skybrian/accordionsynth/sound.h

#include "midi.h"
#include <Audio.h>
#include <AudioStream.h>

namespace sound {

const float cent = 1.0005777;

#define WAVE_COUNT 2
const float detune[WAVE_COUNT] = {-cent*cent, cent*cent};

class Reed {
public:
  Reed(midi::Note n) : note(n) {
    for (int i = 0; i < WAVE_COUNT; i++) {
      waves[i].amplitude(1.0);
      waves[i].frequency(n.frequency() * detune[i]);
      env[i].attack(40);
      env[i].decay(0);
      env[i].sustain(1.0);
      env[i].release(40);
    }
    for (int i = 0; i < WAVE_COUNT; i++) {
      mixer.gain(i, 0.5/WAVE_COUNT);
    }
  }

  bool isActive() {
    return env[0].isActive();
  }

  bool isSustain() {
    return env[0].isSustain();
  }

  bool noteOn() {
    if (isActive()) {
      return false;
    }
    AudioNoInterrupts();
    for (int i = 0; i < WAVE_COUNT; i++) {
      // Start detuned saws slightly out of phase.
      // This doesn't work by default due to a bug:
      // https://github.com/PaulStoffregen/Audio/issues/312
      // I edited the code directly:
      // /Applications/Arduino.app/Contents/Java/hardware/teensy/avr/libraries/Audio/synth_waveform.h
      waves[i].begin(WAVEFORM_SAWTOOTH);
      waves[i].phase(i*20);
      env[i].noteOn();
    }
    AudioInterrupts();
    return true;
  }

  void noteOff() {
    for (int i = 0; i < WAVE_COUNT; i++) {
      env[i].noteOff();
    }
  }

  AudioStream& out() {
    return mixer; 
  }

  midi::Note note;
private:
  AudioSynthWaveform waves[WAVE_COUNT];
  AudioEffectEnvelope env[WAVE_COUNT];
  AudioMixer4 mixer;
  AudioConnection wavePatches[WAVE_COUNT] = {
    AudioConnection(waves[0], 0, env[0], 0),
    AudioConnection(waves[1], 0, env[1], 0),
  };
  AudioConnection envPatches[WAVE_COUNT] = {
    AudioConnection(env[0], 0, mixer, 0),
    AudioConnection(env[1], 0, mixer, 1),
  };
};

#if !defined(__ARM_ARCH_7EM__)
#error "BigMixer not implemented for this platform"
#endif

#define MIXER_SIZE 36

class BigMixer : public AudioStream
{
public:
  BigMixer() : AudioStream(MIXER_SIZE, inputQueueArray) {
    for (int i=0; i<MIXER_SIZE; i++) {
      multiplier[i] = 65536;
      wanted_multiplier[i] = 65536;
    }
  }

  virtual void update(void);

  void gain(unsigned int channel, float gain) {
    if (channel >= MIXER_SIZE) return;
    if (gain > 32767.0f) gain = 32767.0f;
    else if (gain < -32767.0f) gain = -32767.0f;
    wanted_multiplier[channel] = gain * 65536.0f; // TODO: proper roundoff?
  }

  float getGain(unsigned int channel) {
    if (channel >= MIXER_SIZE) return 0;
    return multiplier[channel] / 65536.0f;
  }
  
private:
  int32_t multiplier[MIXER_SIZE];
  int32_t wanted_multiplier[MIXER_SIZE];
  audio_block_t *inputQueueArray[MIXER_SIZE];
};

#define BANK_SIZE MIXER_SIZE

struct ReedBank {
  Reed at[BANK_SIZE];
};

const int doubledNotes = 6;
const int fadeFactor = 2;

class Bank {
private:
  static ReedBank makeReeds(midi::Note n) {
    ReedBank reeds = {{
      Reed(n), Reed(n+1), Reed(n+2), Reed(n+3), Reed(n+4), Reed(n+5),
      Reed(n+6), Reed(n+7), Reed(n+8), Reed(n+9), Reed(n+10), Reed(n+11),
      Reed(n+12), Reed(n+13), Reed(n+14), Reed(n+15), Reed(n+16), Reed(n+17),
      Reed(n+18), Reed(n+19), Reed(n+20), Reed(n+21), Reed(n+22), Reed(n+23),
      Reed(n+24), Reed(n+25), Reed(n+26), Reed(n+27), Reed(n+28), Reed(n+29),
      Reed(n+30), Reed(n+31), Reed(n+32), Reed(n+33), Reed(n+34), Reed(n+35)
    }};
    return reeds;
  }

public:
  Bank(midi::Note n) : reeds(makeReeds(n)) {
  }

  void notesOn(midi::Chord chord) {
    midi::Chord orig = chord;

    // double the bottom notes
    for (int i = 0; i<doubledNotes; i++) {
      midi::Note n = reeds.at[i].note;
      if (chord.has(n)) {
        chord = chord + (n + 12);
      }
    }

    int noteCount = 0;
    for (int i = 0; i<BANK_SIZE; i++) {
      midi::Note n = reeds.at[i].note;
      if (chord.has(n)) {
        reeds.at[i].noteOn();
        noteCount++;
      } else if (prev.has(n)) {
        // noteOff is not idempoent. See: https://github.com/PaulStoffregen/Audio/issues/311
        reeds.at[i].noteOff();
      }
    }
    if (noteCount > 0) {
      float gain = 0.8/(noteCount+5);
      for (int i = 0; i<BANK_SIZE; i++) {
        float g = gain;
        if (i < doubledNotes) {
          // Fade the bottom notes for a Shepard tone effect.
          g = g * (float)(i+doubledNotes*(fadeFactor-1))/(doubledNotes*fadeFactor);
        } else if (i >= 12 && i < 12 + doubledNotes && !orig.has(reeds.at[i].note)) {
          // Fade the doubled notes unless they were originally played.
          g = g * (float)(doubledNotes*fadeFactor-(i-12))/(doubledNotes*fadeFactor);
        }
        mixer.gain(i, g);
      }
    }
    prev = chord;
  }

  void notesOff() {
    notesOn(midi::Chord());
  }

  void plotReedState(Print& out, midi::Note note) {
    midi::Note base = reeds.at[0].note;
    signed char index = note - base;
    if (index < 0 || index > BANK_SIZE) return;

    int active = reeds.at[index].isActive() ? 1 : 0;
    int sustain = reeds.at[index].isSustain() ? 1 : 0;
    float gain = mixer.getGain(index);
    out.print(active);
    out.print(" ");
    out.print(sustain);
    out.print(" ");
    out.println(gain);
  }

  AudioStream& out() {
    return mixer; 
  }  
  
private:
  ReedBank reeds;
  BigMixer mixer;
  midi::Chord prev;
  AudioConnection patches[BANK_SIZE] = {
    AudioConnection(reeds.at[0].out(), 0, mixer, 0),
    AudioConnection(reeds.at[1].out(), 0, mixer, 1),
    AudioConnection(reeds.at[2].out(), 0, mixer, 2),
    AudioConnection(reeds.at[3].out(), 0, mixer, 3),
    AudioConnection(reeds.at[4].out(), 0, mixer, 4),
    AudioConnection(reeds.at[5].out(), 0, mixer, 5),
    AudioConnection(reeds.at[6].out(), 0, mixer, 6),
    AudioConnection(reeds.at[7].out(), 0, mixer, 7),
    AudioConnection(reeds.at[8].out(), 0, mixer, 8),
    AudioConnection(reeds.at[9].out(), 0, mixer, 9),
    AudioConnection(reeds.at[10].out(), 0, mixer, 10),
    AudioConnection(reeds.at[11].out(), 0, mixer, 11),
    AudioConnection(reeds.at[12].out(), 0, mixer, 12),
    AudioConnection(reeds.at[13].out(), 0, mixer, 13),
    AudioConnection(reeds.at[14].out(), 0, mixer, 14),
    AudioConnection(reeds.at[15].out(), 0, mixer, 15),
    AudioConnection(reeds.at[16].out(), 0, mixer, 16),
    AudioConnection(reeds.at[17].out(), 0, mixer, 17),
    AudioConnection(reeds.at[18].out(), 0, mixer, 18),
    AudioConnection(reeds.at[19].out(), 0, mixer, 19),
    AudioConnection(reeds.at[20].out(), 0, mixer, 20),
    AudioConnection(reeds.at[21].out(), 0, mixer, 21),
    AudioConnection(reeds.at[22].out(), 0, mixer, 22),
    AudioConnection(reeds.at[23].out(), 0, mixer, 23),
    AudioConnection(reeds.at[24].out(), 0, mixer, 24),
    AudioConnection(reeds.at[25].out(), 0, mixer, 25),
    AudioConnection(reeds.at[26].out(), 0, mixer, 26),
    AudioConnection(reeds.at[27].out(), 0, mixer, 27),
    AudioConnection(reeds.at[28].out(), 0, mixer, 28),
    AudioConnection(reeds.at[29].out(), 0, mixer, 29),
    AudioConnection(reeds.at[30].out(), 0, mixer, 30),
    AudioConnection(reeds.at[31].out(), 0, mixer, 31),
    AudioConnection(reeds.at[32].out(), 0, mixer, 32),
    AudioConnection(reeds.at[33].out(), 0, mixer, 33),
    AudioConnection(reeds.at[34].out(), 0, mixer, 34),
    AudioConnection(reeds.at[35].out(), 0, mixer, 35)
  };
};

} // namespace
